DannyJusvin/Front-End-Power-Protection/Simulation (LTspice)/Draft9.asc

C1: cap; 100n
Ccomp: cap; 100p
Cg: cap; 4.7µ
Cload: cap; 470µ
D1: diode; Dmbr745
D2: zener; 1N4744A
D3: zener; 1N4733A
M1: pmos; IRF4905
Q1: pnp; 2N3906
Rbase: res; 4.7k
Rbottom: res; 13k
Rg: res; 36k
Rhys: res; 600k
Rload: res; 10
Rpull: res; 10k
Rref: res; 10k
Rstep: res; 10k
Rtop: res; 22k
Rz: res; 1k
U1: LM2903B
V1: voltage; PWL(0 0 50m 12 200m 12 350m 15 500m 12)
Named nets: 0, VIN_PROT, Vout, VIN, LM393_OUT, GATE, IN+, IN-
.tran 0 500m
.include irf4905.spi
.model 1N4733A D(Is=1.214f Rs=1.078 Ikf=0 N=1 Xti=3 Eg=1.11 Cjo=185p 
+ M=.3509 Vj=.75 Fc=.5 Isr=2.601n Nr=2 Bv=5.1 Ibv=.70507 
+ Nbv=.74348 Ibvl=4.8274m Nbvl=6.7393 Tbv1=176.471u)
.model 1N4744A D(Is=1.408n Rs=0.1 N=1 Xti=3 Eg=1.11 Cjo=120p M=0.3333 Vj=0.75 Fc=0.5 Isr=10n Nr=2 Bv=15 Ibv=0.017 Nbv=1.5 Tnom=27)
.lib MBR745.lib
