DannyJusvin/Front-End-Power-Protection/KiCad Prototype (THT)/Blind_Spot_Detection_System.kicad_sch

## KiCad design KiCad Prototype (THT)/Blind_Spot_Detection_System.kicad_sch (2026-08-07)

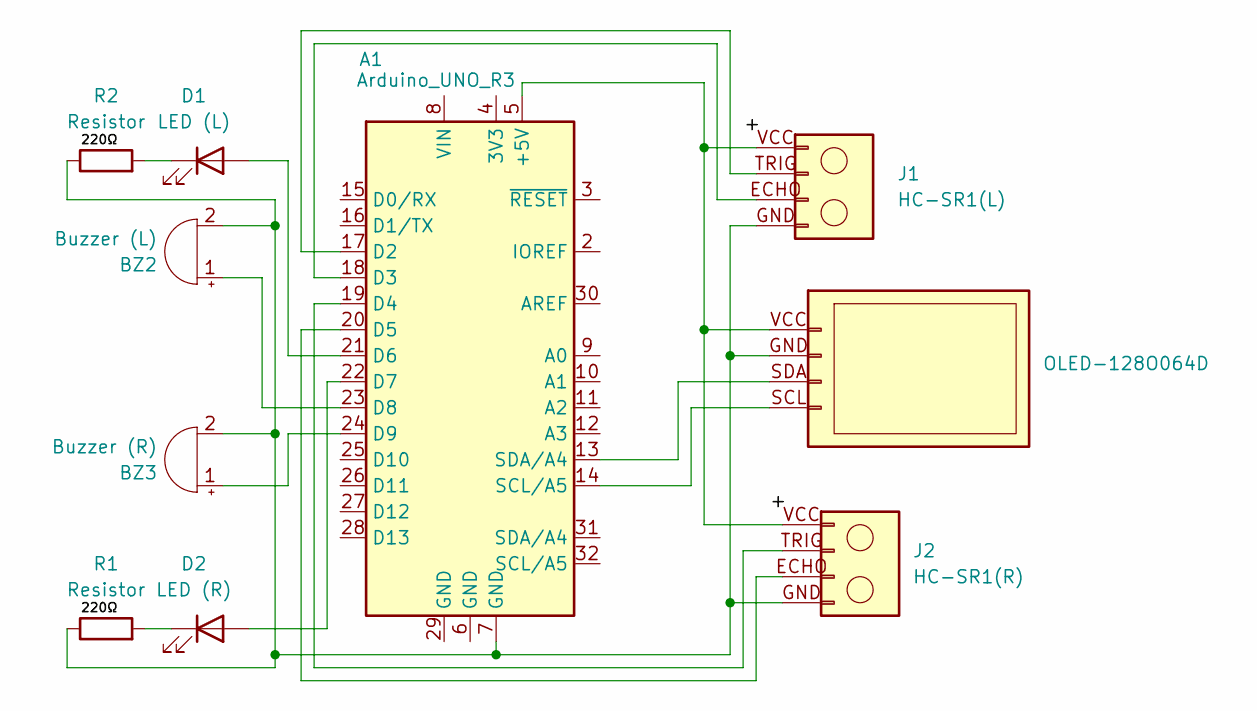
[picture p15: schematic Blind_Spot_Detection_System.kicad_sch]

Parts:
A1: Arduino_UNO_R3
BZ2: Buzzer (L)
BZ3: Buzzer (R)
D1: LED (L)
D2: LED (R)
J1: HC-SR1(L)
J2: HC-SR1(R)
OLED-128O064D: Conn_01x04
R1, R2: Resistor

Connections:
unnamed: A1.5 (+5V), J1.VCC (Pin_1), J2.VCC (Pin_1), OLED-128O064D.VCC (Pin_1)
unnamed: A1.7 (GND), BZ2.2 (-), BZ3.2 (-), J1.GND (Pin_4), J2.GND (Pin_4), OLED-128O064D.GND (Pin_2), R1.1, R2.1
unnamed: A1.13 (SDA/A4), OLED-128O064D.SDA (Pin_3)
unnamed: A1.14 (SCL/A5), OLED-128O064D.SCL (SCLPin_4)
unnamed: A1.17 (D2), J1.TRIG (Pin_2)
unnamed: A1.18 (D3), J1.ECHO (Pin_3)
unnamed: A1.19 (D4), J2.TRIG (Pin_2)
unnamed: A1.20 (D5), J2.ECHO (Pin_3)
unnamed: A1.21 (D6), D1.2 (A)
unnamed: A1.22 (D7), D2.2 (A)
unnamed: A1.23 (D8), BZ2.1 (+)
unnamed: A1.24 (D9), BZ3.1 (+)
unnamed: D1.1 (K), R2.2
unnamed: D2.1 (K), R1.2
